NicolasAdell/SolarTracker/circuitos/Placa Panel esquematico.kicad_sch

## KiCad design circuitos/Placa Panel esquematico.kicad_sch (2023-11-17)

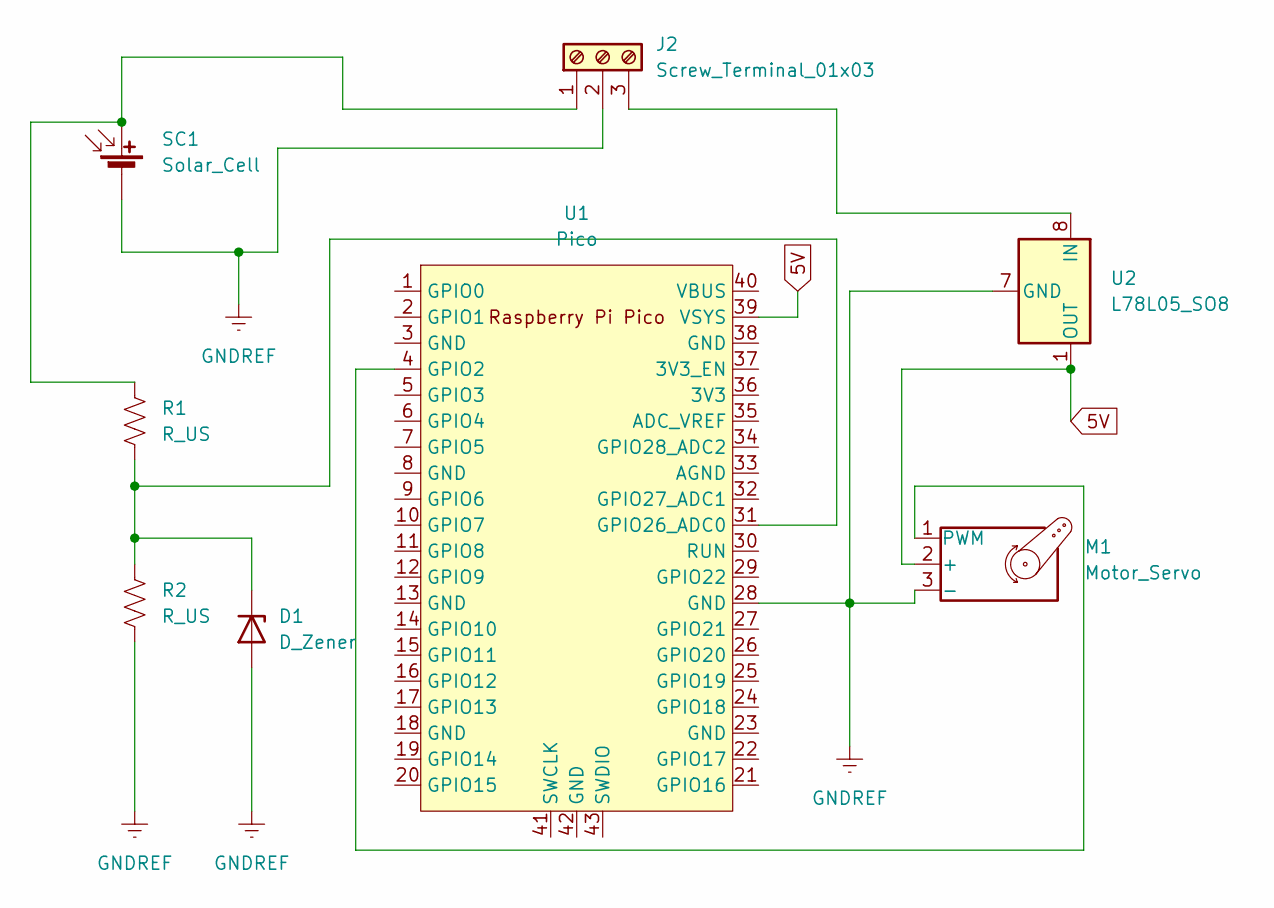
[picture p15: schematic Placa Panel esquematico.kicad_sch]

Parts:
D1: D_Zener; D_A-405_P7.62mm_Horizontal
J2: Screw_Terminal_01x03; PinSocket_1x03_P1.27mm_Vertical
M1: Motor_Servo; PinSocket_1x03_P1.27mm_Vertical
R1, R2: R_US; R_Axial_DIN0204_L3.6mm_D1.6mm_P5.08mm_Horizontal
SC1: Solar_Cell; LairdTech_28C0236-0JW-10
U1: Pico; RPi_Pico_SMD_TH
U2: L78L05_SO8; PinHeader_1x03_P1.27mm_Vertical

Connections:
5V: M1.2 (+), U1.39 (VSYS), U2.1 (OUT)
GNDREF: D1.2 (A), J2.2, M1.3 (-), R2.2, SC1.2 (-), U1.28 (GND), U2.2 (GND), U2.3 (GND), U2.6 (GND), U2.7 (GND)
unnamed: D1.1 (K), R1.2, R2.1, U1.31 (GPIO26_ADC0)
unnamed: J2.1, R1.1, SC1.1 (+)
unnamed: J2.3, U2.8 (IN)
unnamed: M1.1 (PWM), U1.4 (GPIO2)
